danmar/mobilephone/images/2.jpg

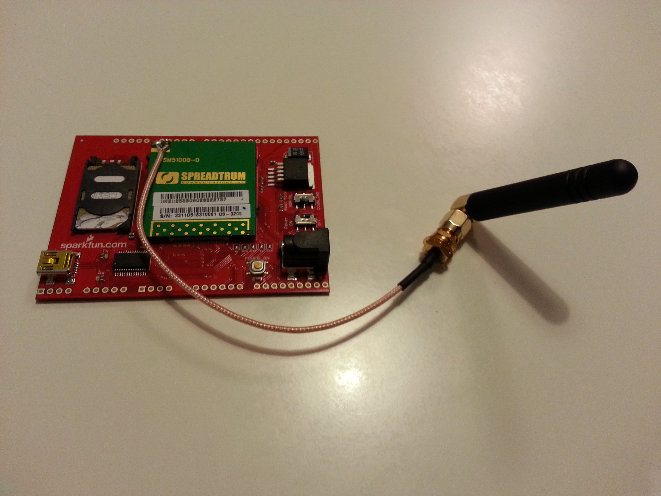
images/2.jpg
